robsonsmartins/usbflashprog/docs/firmware/html/a00003.png

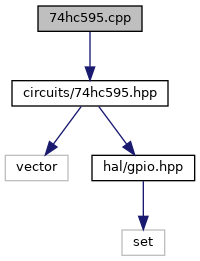
docs/firmware/html/a00003.png
