robsonsmartins/usbflashprog/docs/firmware/html/a00006.png

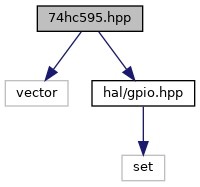
docs/firmware/html/a00006.png
