robsonsmartins/usbflashprog/docs/firmware/html/a00012.png

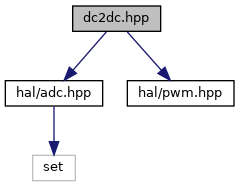
docs/firmware/html/a00012.png
