robsonsmartins/usbflashprog/docs/firmware/html/a00015.png

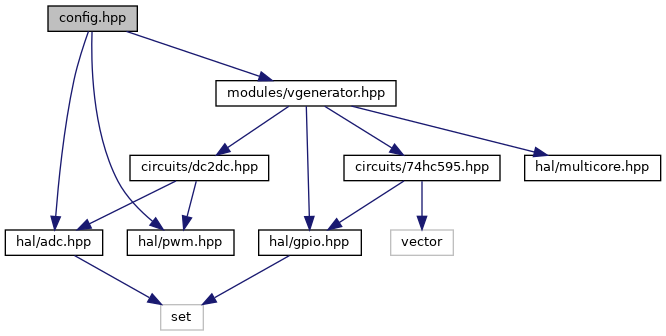
docs/firmware/html/a00015.png
