robsonsmartins/usbflashprog/docs/firmware/html/a00048.png

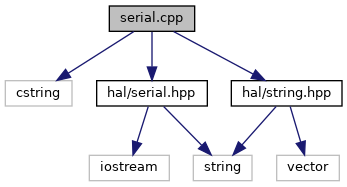
docs/firmware/html/a00048.png
