robsonsmartins/usbflashprog/docs/firmware/html/a00060.png

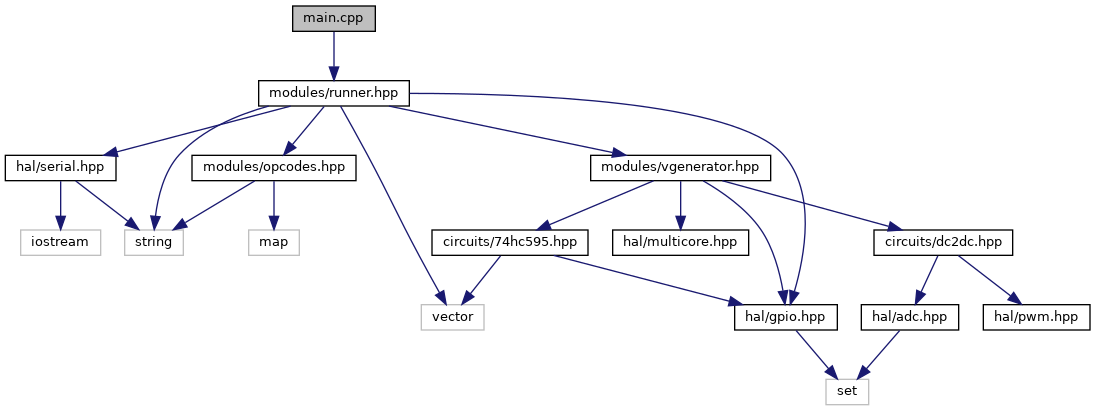
docs/firmware/html/a00060.png
