robsonsmartins/usbflashprog/docs/firmware/html/a00063.png

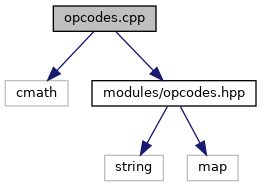
docs/firmware/html/a00063.png
