robsonsmartins/usbflashprog/docs/firmware/html/a00069.png

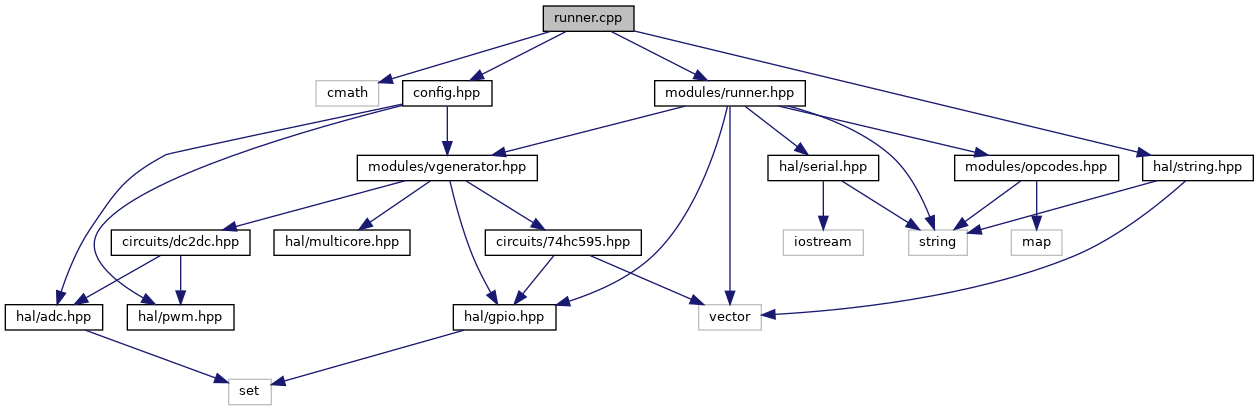
docs/firmware/html/a00069.png
