robsonsmartins/usbflashprog/docs/firmware/html/a00075.png

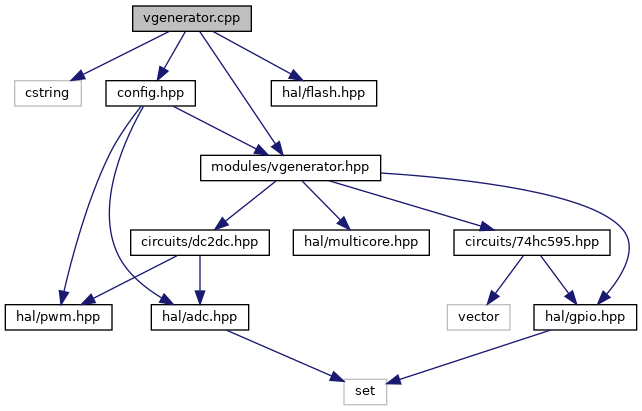
docs/firmware/html/a00075.png
