robsonsmartins/usbflashprog/docs/firmware/html/a00078.png

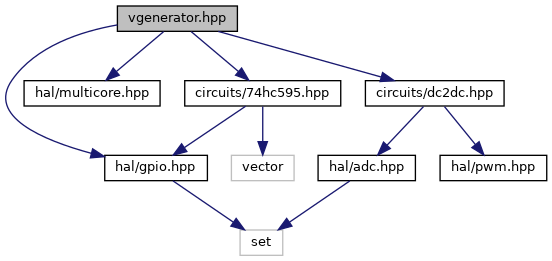
docs/firmware/html/a00078.png
