robsonsmartins/usbflashprog/docs/firmware/html/a00084.png

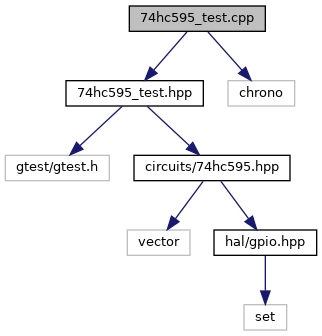
docs/firmware/html/a00084.png
