robsonsmartins/usbflashprog/docs/firmware/html/a00087.png

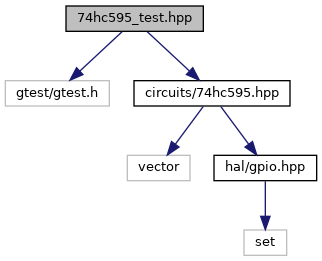
docs/firmware/html/a00087.png
