robsonsmartins/usbflashprog/docs/firmware/html/a00096.png

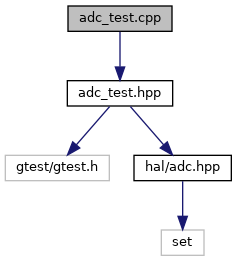
docs/firmware/html/a00096.png
