robsonsmartins/usbflashprog/docs/firmware/html/a00099.png

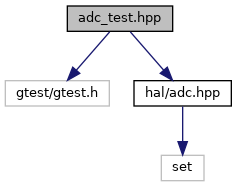
docs/firmware/html/a00099.png
