robsonsmartins/usbflashprog/docs/firmware/html/a00102.png

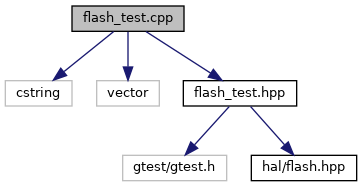
docs/firmware/html/a00102.png
