robsonsmartins/usbflashprog/docs/firmware/html/a00114.png

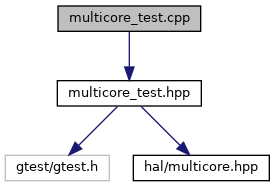
docs/firmware/html/a00114.png
