robsonsmartins/usbflashprog/docs/firmware/html/a00120.png

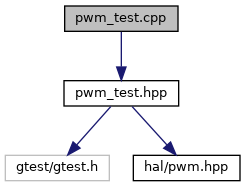
docs/firmware/html/a00120.png
