robsonsmartins/usbflashprog/docs/firmware/html/a00126.png

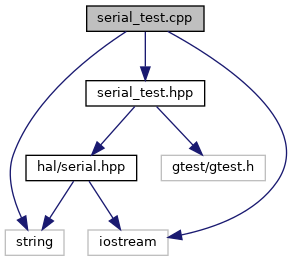
docs/firmware/html/a00126.png
