robsonsmartins/usbflashprog/docs/firmware/html/a00129.png

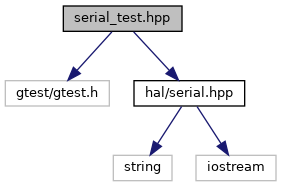
docs/firmware/html/a00129.png
