robsonsmartins/usbflashprog/docs/firmware/html/a00132.png

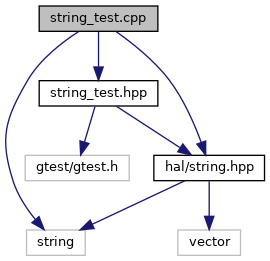
docs/firmware/html/a00132.png
