robsonsmartins/usbflashprog/docs/firmware/html/a00135.png

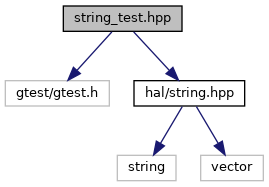
docs/firmware/html/a00135.png
