robsonsmartins/usbflashprog/docs/firmware/html/a00165.png

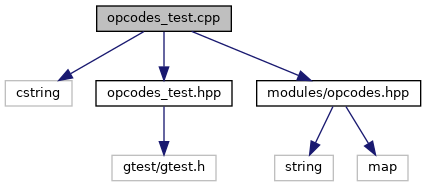
docs/firmware/html/a00165.png
