robsonsmartins/usbflashprog/docs/firmware/html/a00171.png

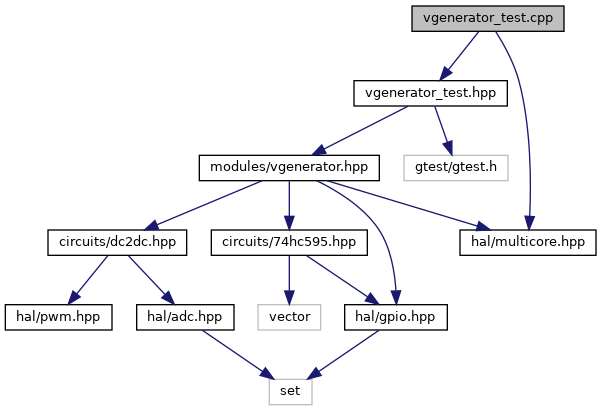
docs/firmware/html/a00171.png
