robsonsmartins/usbflashprog/docs/firmware/html/a00174.png

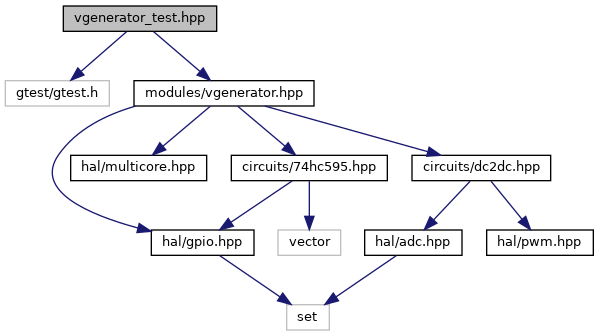
docs/firmware/html/a00174.png
