robsonsmartins/usbflashprog/docs/firmware/html/a00944.png

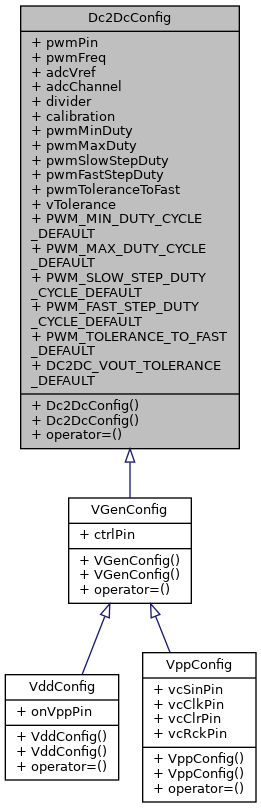
docs/firmware/html/a00944.png
