robsonsmartins/usbflashprog/docs/firmware/html/a00976.png

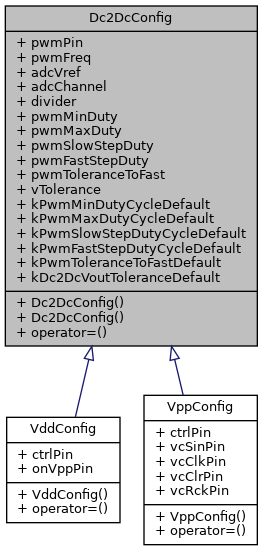
docs/firmware/html/a00976.png
