robsonsmartins/usbflashprog/docs/firmware/html/a01045.png

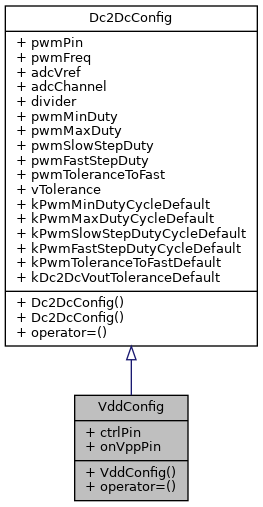
docs/firmware/html/a01045.png
