robsonsmartins/usbflashprog/docs/firmware/html/a01049.png

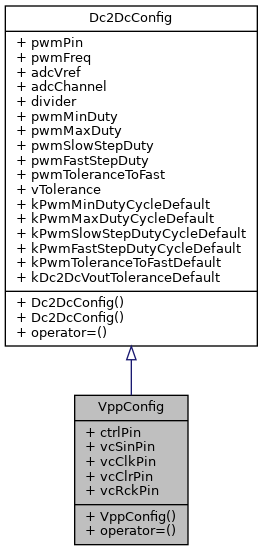
docs/firmware/html/a01049.png
