robsonsmartins/usbflashprog/docs/firmware/html/a01057.png

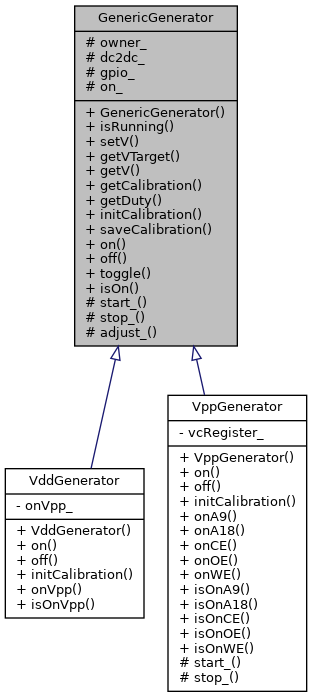
docs/firmware/html/a01057.png
