robsonsmartins/usbflashprog/docs/firmware/html/dir_73c31730a899c84a7a5c88cb9143c198_dep.png

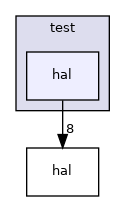
docs/firmware/html/dir_73c31730a899c84a7a5c88cb9143c198_dep.png
