robsonsmartins/usbflashprog/docs/firmware/html/dir_e05d7e2b1ecd646af5bb94391405f3b5_dep.png

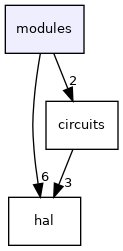
docs/firmware/html/dir_e05d7e2b1ecd646af5bb94391405f3b5_dep.png
