robsonsmartins/usbflashprog/docs/firmware/html/dir_fb26c1e57a9d2d92e8844fee7346a524_dep.png

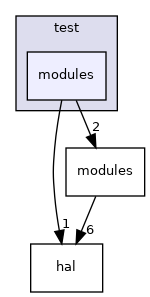
docs/firmware/html/dir_fb26c1e57a9d2d92e8844fee7346a524_dep.png
