robsonsmartins/usbflashprog/docs/software/html/a00009.png

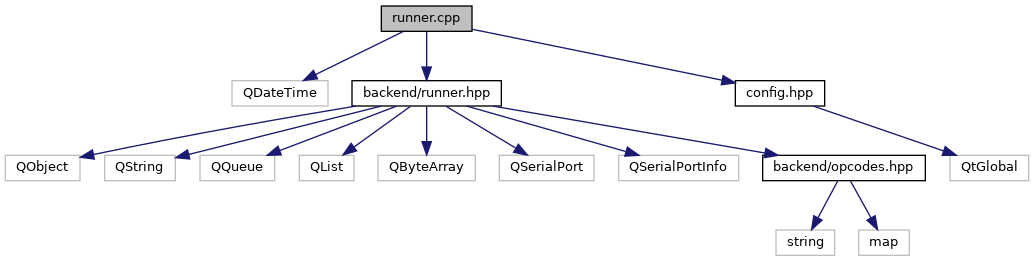
docs/software/html/a00009.png
