robsonsmartins/usbflashprog/docs/software/html/a00018.png

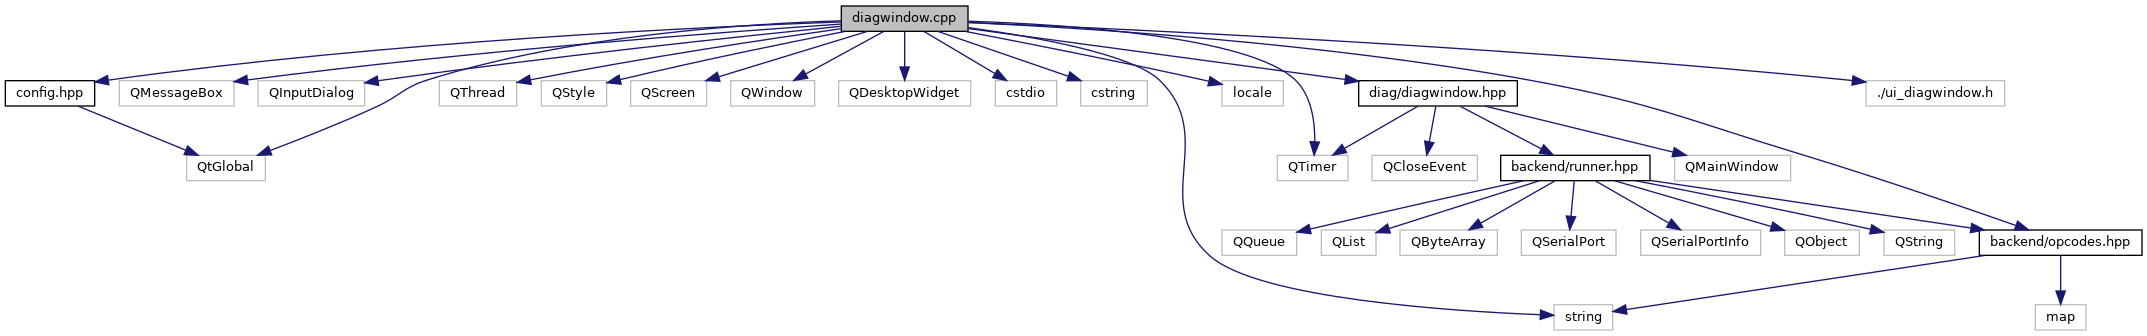
docs/software/html/a00018.png
