robsonsmartins/usbflashprog/docs/software/html/a00021.png

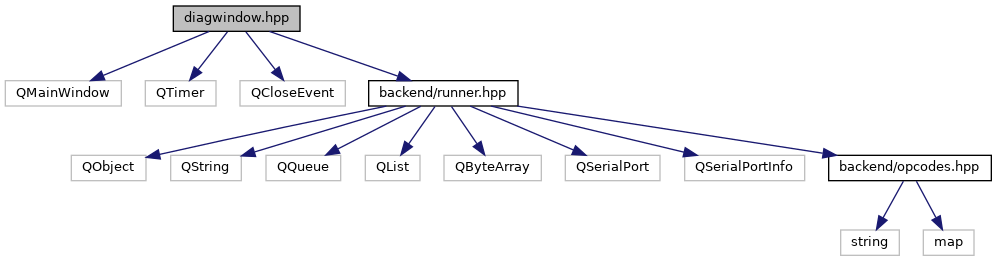
docs/software/html/a00021.png
