robsonsmartins/usbflashprog/docs/software/html/a00024.png

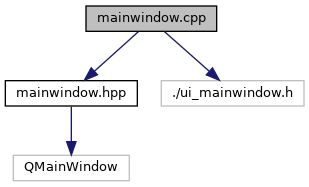
docs/software/html/a00024.png
