robsonsmartins/usbflashprog/docs/software/html/a00030.png

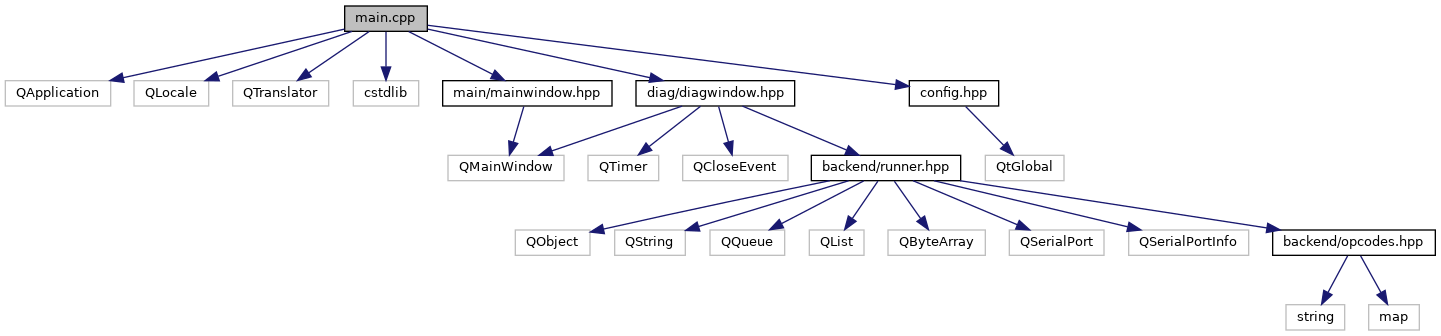
docs/software/html/a00030.png
