robsonsmartins/usbflashprog/docs/software/html/dir_13e138d54eb8818da29c3992edef070a_dep.png

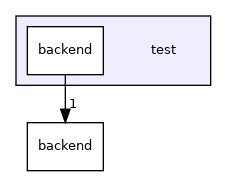
docs/software/html/dir_13e138d54eb8818da29c3992edef070a_dep.png
