robsonsmartins/usbflashprog/software/usbflashprog/scripts/ufprog.bmp

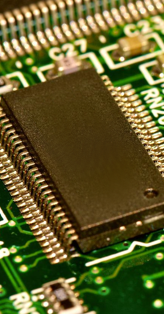
software/usbflashprog/scripts/ufprog.bmp
