robsonsmartins/usbflashprog/hardware/usbflashprog.kicad_pcb

## KiCad design hardware/usbflashprog.kicad_pcb (2022-05-16)

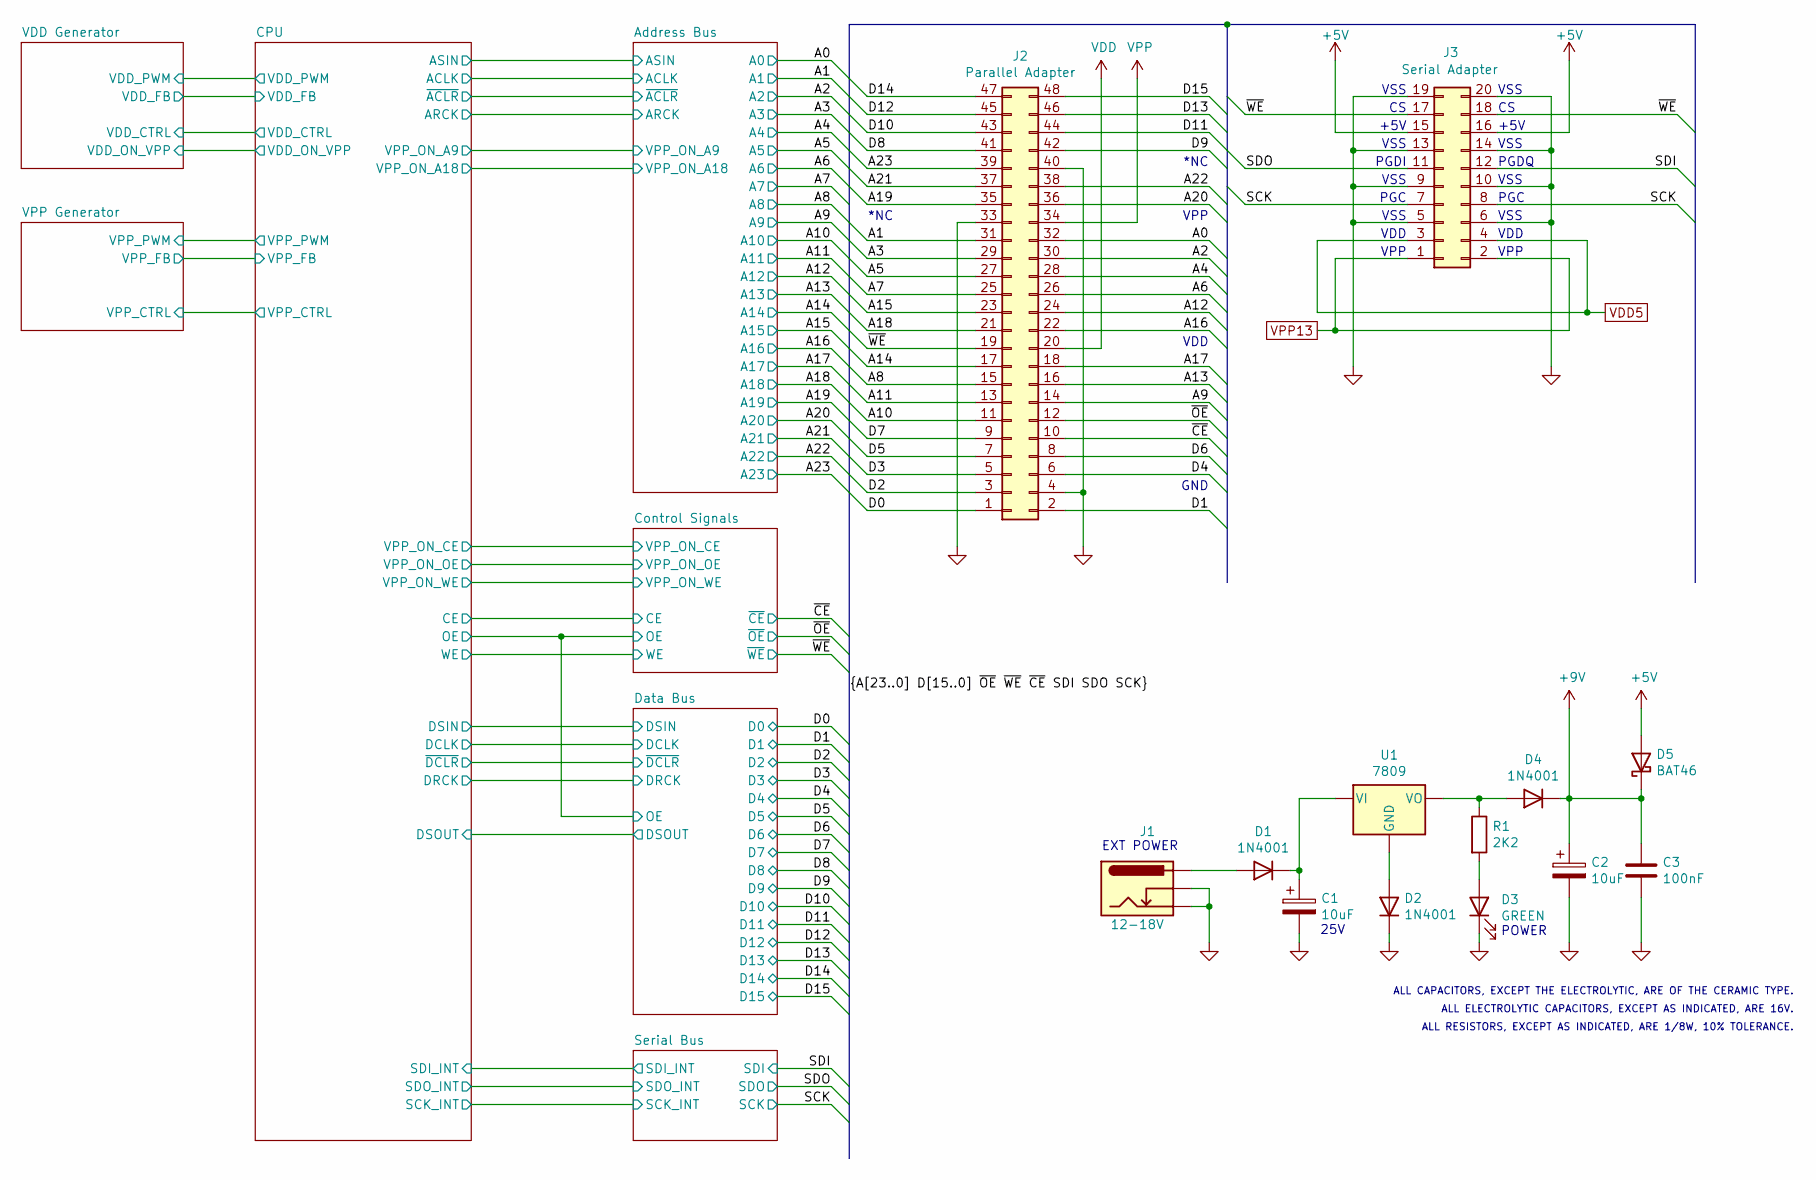
[picture p56: schematic usbflashprog.kicad_sch, USB Flash/EPROM Programmer]

Parts:
C1, C2: 10uF; CP_Radial_D5.0mm_P2.50mm
C3: 100nF; C_Disc_D6.0mm_W2.5mm_P5.00mm
D1, D2, D4: 1N4001; D_DO-41_SOD81_P10.16mm_Horizontal
D3: GREEN; LED_D3.0mm
D5: BAT46; D_DO-35_SOD27_P7.62mm_Horizontal
J1: 12-18V; BarrelJack_Horizontal
J2: Parallel Adapter; PinSocket_2x24_P2.54mm_Vertical
J3: Serial Adapter; PinSocket_2x10_P2.54mm_Vertical
R1: 2K2; R_Axial_DIN0207_L6.3mm_D2.5mm_P10.16mm_Horizontal
U1: 7809; TO-220-3_Vertical

Connections:
+5V: D5.2 (A), J3.15, J3.16; also elsewhere on the board
+9V: C2.1, C3.1, D4.1 (K), D5.1 (K); also elsewhere on the board
/A0: J2.32; also elsewhere on the board
/A1: J2.31; also elsewhere on the board
/A2: J2.30; also elsewhere on the board
/A3: J2.29; also elsewhere on the board
/A4: J2.28; also elsewhere on the board
/A5: J2.27; also elsewhere on the board
/A6: J2.26; also elsewhere on the board
/A7: J2.25; also elsewhere on the board
/A8: J2.15; also elsewhere on the board
/A9: J2.14; also elsewhere on the board
/A10: J2.11; also elsewhere on the board
/A11: J2.13; also elsewhere on the board
/A12: J2.24; also elsewhere on the board
/A13: J2.16; also elsewhere on the board
/A14: J2.17; also elsewhere on the board
/A15: J2.23; also elsewhere on the board
/A16: J2.22; also elsewhere on the board
/A17: J2.18; also elsewhere on the board
/A18: J2.21; also elsewhere on the board
/A19: J2.35; also elsewhere on the board
/A20: J2.36; also elsewhere on the board
/A21: J2.37; also elsewhere on the board
/A22: J2.38; also elsewhere on the board
/A23: J2.39; also elsewhere on the board
/D0: J2.1; also elsewhere on the board
/D1: J2.2; also elsewhere on the board
/D2: J2.3; also elsewhere on the board
/D3: J2.5; also elsewhere on the board
/D4: J2.6; also elsewhere on the board
/D5: J2.7; also elsewhere on the board
/D6: J2.8; also elsewhere on the board
/D7: J2.9; also elsewhere on the board
/D8: J2.41; also elsewhere on the board
/D9: J2.42; also elsewhere on the board
/D10: J2.43; also elsewhere on the board
/D11: J2.44; also elsewhere on the board
/D12: J2.45; also elsewhere on the board
/D13: J2.46; also elsewhere on the board
/D14: J2.47; also elsewhere on the board
/D15: J2.48; also elsewhere on the board
/SCK: J3.7, J3.8; also elsewhere on the board
/SDI: J3.12; also elsewhere on the board
/SDO: J3.11; also elsewhere on the board
/~CE: J2.10; also elsewhere on the board
/~OE: J2.12; also elsewhere on the board
/~WE: J2.19, J3.17, J3.18; also elsewhere on the board
GND: C1.2, C2.2, C3.2, D2.1 (K), D3.1 (K), J1.2, J1.3, J2.4, J2.33, J2.40, J3.5, J3.6, J3.9, J3.10, J3.13, J3.14, J3.19, J3.20; also elsewhere on the board
unnamed: C1.1, D1.1 (K), U1.1 (VI)
unnamed: D1.2 (A), J1.1
unnamed: D2.2 (A), U1.2 (GND)
unnamed: D3.2 (A), R1.2
unnamed: D4.2 (A), R1.1, U1.3 (VO)
VDD: J2.20; also elsewhere on the board
VDD5: J3.3, J3.4; also elsewhere on the board
VPP: J2.34; also elsewhere on the board
VPP13: J3.1, J3.2; also elsewhere on the board

Notes on the sheet:
EXT POWER
+5V
VSS
PGC
VPP
25V
*NC
POWER
VDD
ALL CAPACITORS, EXCEPT THE ELECTROLYTIC, ARE OF THE CERAMIC TYPE.
ALL RESISTORS, EXCEPT AS INDICATED, ARE 1/8W, 10% TOLERANCE.
PGDI
PGDQ
GND
ALL ELECTROLYTIC CAPACITORS, EXCEPT AS INDICATED, ARE 16V.

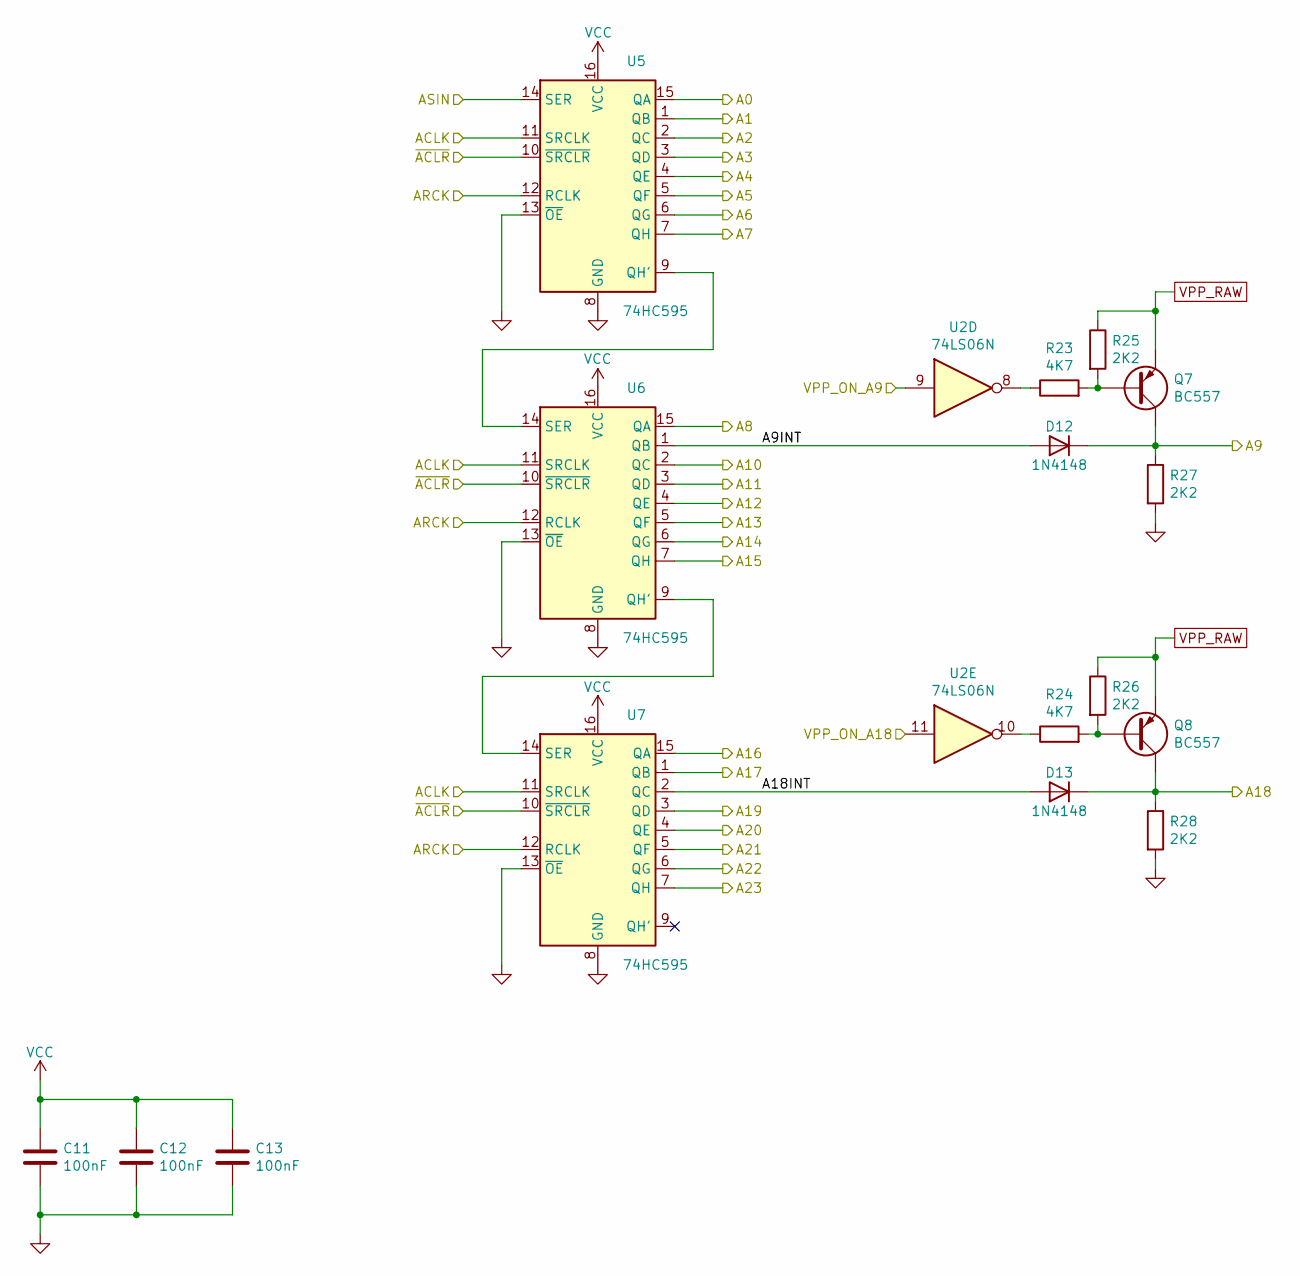
[picture p57: schematic address_bus.kicad_sch, USB Flash/EPROM Programmer]

Parts:
C11, C12, C13: 100nF; C_Disc_D6.0mm_W2.5mm_P5.00mm
D12, D13: 1N4148; D_DO-35_SOD27_P7.62mm_Horizontal
Q7, Q8: BC557; TO-92_Inline_Wide
R23, R24: 4K7; R_Axial_DIN0207_L6.3mm_D2.5mm_P10.16mm_Horizontal
R25, R26, R27, R28: 2K2; R_Axial_DIN0207_L6.3mm_D2.5mm_P10.16mm_Horizontal
U2: 74LS06N; DIP-14_W7.62mm
U5, U6, U7: 74HC595; DIP-16_W7.62mm

Connections:
/A0: U5.15 (QA); also elsewhere on the board
/A1: U5.1 (QB); also elsewhere on the board
/A2: U5.2 (QC); also elsewhere on the board
/A3: U5.3 (QD); also elsewhere on the board
/A4: U5.4 (QE); also elsewhere on the board
/A5: U5.5 (QF); also elsewhere on the board
/A6: U5.6 (QG); also elsewhere on the board
/A7: U5.7 (QH); also elsewhere on the board
/A8: U6.15 (QA); also elsewhere on the board
/A9: D12.1 (K), Q7.1 (C), R27.1; also elsewhere on the board
/A10: U6.2 (QC); also elsewhere on the board
/A11: U6.3 (QD); also elsewhere on the board
/A12: U6.4 (QE); also elsewhere on the board
/A13: U6.5 (QF); also elsewhere on the board
/A14: U6.6 (QG); also elsewhere on the board
/A15: U6.7 (QH); also elsewhere on the board
/A16: U7.15 (QA); also elsewhere on the board
/A17: U7.1 (QB); also elsewhere on the board
/A18: D13.1 (K), Q8.1 (C), R28.1; also elsewhere on the board
/A19: U7.3 (QD); also elsewhere on the board
/A20: U7.4 (QE); also elsewhere on the board
/A21: U7.5 (QF); also elsewhere on the board
/A22: U7.6 (QG); also elsewhere on the board
/A23: U7.7 (QH); also elsewhere on the board
/Address Bus/A9INT: D12.2 (A), U6.1 (QB)
/Address Bus/A18INT: D13.2 (A), U7.2 (QC)
/Address Bus/ACLK: U5.11 (SRCLK), U6.11 (SRCLK), U7.11 (SRCLK); also elsewhere on the board
/Address Bus/ARCK: U5.12 (RCLK), U6.12 (RCLK), U7.12 (RCLK); also elsewhere on the board
/Address Bus/ASIN: U5.14 (SER); also elsewhere on the board
/Address Bus/VPP_ON_A9: U2.9; also elsewhere on the board
/Address Bus/VPP_ON_A18: U2.11; also elsewhere on the board
/Address Bus/~ACLR: U5.10 (~SRCLR), U6.10 (~SRCLR), U7.10 (~SRCLR); also elsewhere on the board
GND: C11.2, C12.2, C13.2, R27.2, R28.2, U5.8 (GND), U5.13 (~OE), U6.8 (GND), U6.13 (~OE), U7.8 (GND), U7.13 (~OE); also elsewhere on the board
unnamed: Q7.2 (B), R23.2, R25.2
unnamed: Q8.2 (B), R24.2, R26.2
unnamed: R23.1, U2.8
unnamed: R24.1, U2.10
unnamed: U5.9 (QH'), U6.14 (SER)
unnamed: U6.9 (QH'), U7.14 (SER)
VCC: C11.1, C12.1, C13.1, U5.16 (VCC), U6.16 (VCC), U7.16 (VCC); also elsewhere on the board
VPP_RAW: Q7.3 (E), Q8.3 (E), R25.1, R26.1; also elsewhere on the board

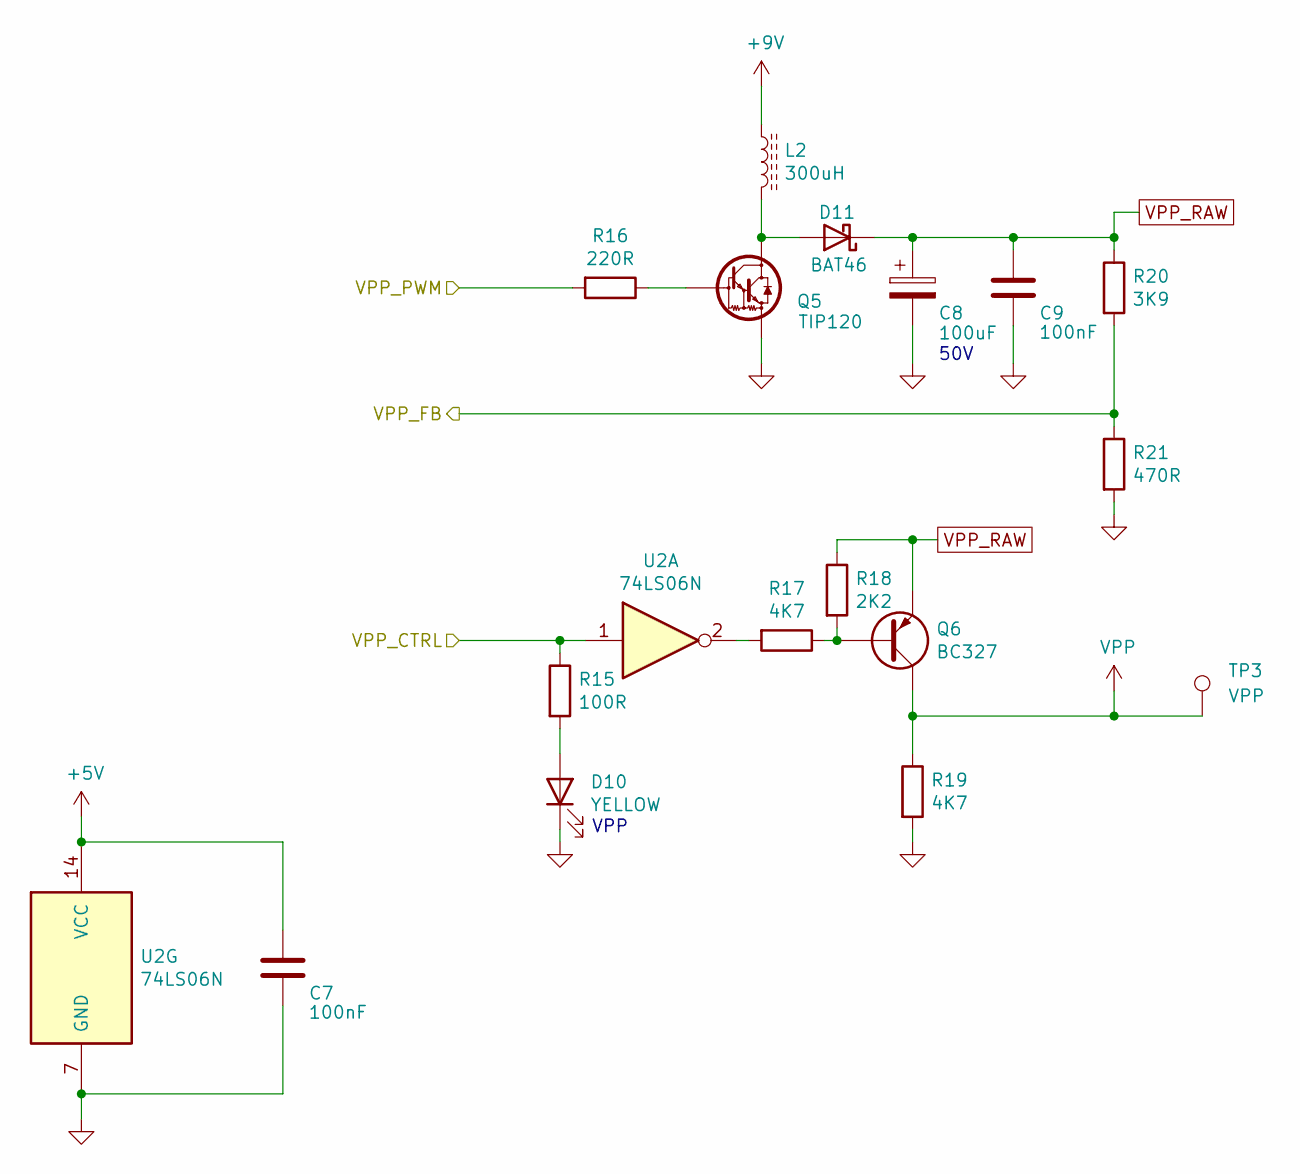
[picture p58: schematic vpp_generator.kicad_sch, USB Flash/EPROM Programmer]

Parts:
C7, C9: 100nF; C_Disc_D6.0mm_W2.5mm_P5.00mm
C8: 100uF; CP_Radial_D8.0mm_P3.50mm
D10: YELLOW; LED_D3.0mm
D11: BAT46; D_DO-35_SOD27_P7.62mm_Horizontal
L2: 300uH; L_Toroid_Vertical_L13.0mm_W6.5mm_P5.60mm
Q5: TIP120; TO-220-3_Vertical
Q6: BC327; TO-92_Inline_Wide
R15: 100R; R_Axial_DIN0207_L6.3mm_D2.5mm_P10.16mm_Horizontal
R16: 220R; R_Axial_DIN0207_L6.3mm_D2.5mm_P10.16mm_Horizontal
R17, R19: 4K7; R_Axial_DIN0207_L6.3mm_D2.5mm_P10.16mm_Horizontal
R18: 2K2; R_Axial_DIN0207_L6.3mm_D2.5mm_P10.16mm_Horizontal
R20: 3K9; R_Axial_DIN0207_L6.3mm_D2.5mm_P10.16mm_Horizontal
R21: 470R; R_Axial_DIN0207_L6.3mm_D2.5mm_P10.16mm_Horizontal
TP3: VPP; TestPoint_THTPad_2.5x2.5mm_Drill1.2mm
U2: 74LS06N; DIP-14_W7.62mm

Connections:
+5V: C7.1, U2.14 (VCC); also elsewhere on the board
+9V: L2.1; also elsewhere on the board
/CPU/VPP_CTRL: R15.1, U2.1; also elsewhere on the board
/CPU/VPP_FB: R20.2, R21.1; also elsewhere on the board
/CPU/VPP_PWM: R16.2; also elsewhere on the board
GND: C7.2, C8.2, C9.2, D10.1 (K), Q5.3 (E), R19.2, R21.2, U2.7 (GND); also elsewhere on the board
unnamed: D10.2 (A), R15.2
unnamed: D11.2 (A), L2.2, Q5.2 (C)
unnamed: Q5.1 (B), R16.1
unnamed: Q6.2 (B), R17.1, R18.2
unnamed: R17.2, U2.2
VPP: Q6.1 (C), R19.1, TP3.1; also elsewhere on the board
VPP_RAW: C8.1, C9.1, D11.1 (K), Q6.3 (E), R18.1, R20.1; also elsewhere on the board

Notes on the sheet:
VPP
50V

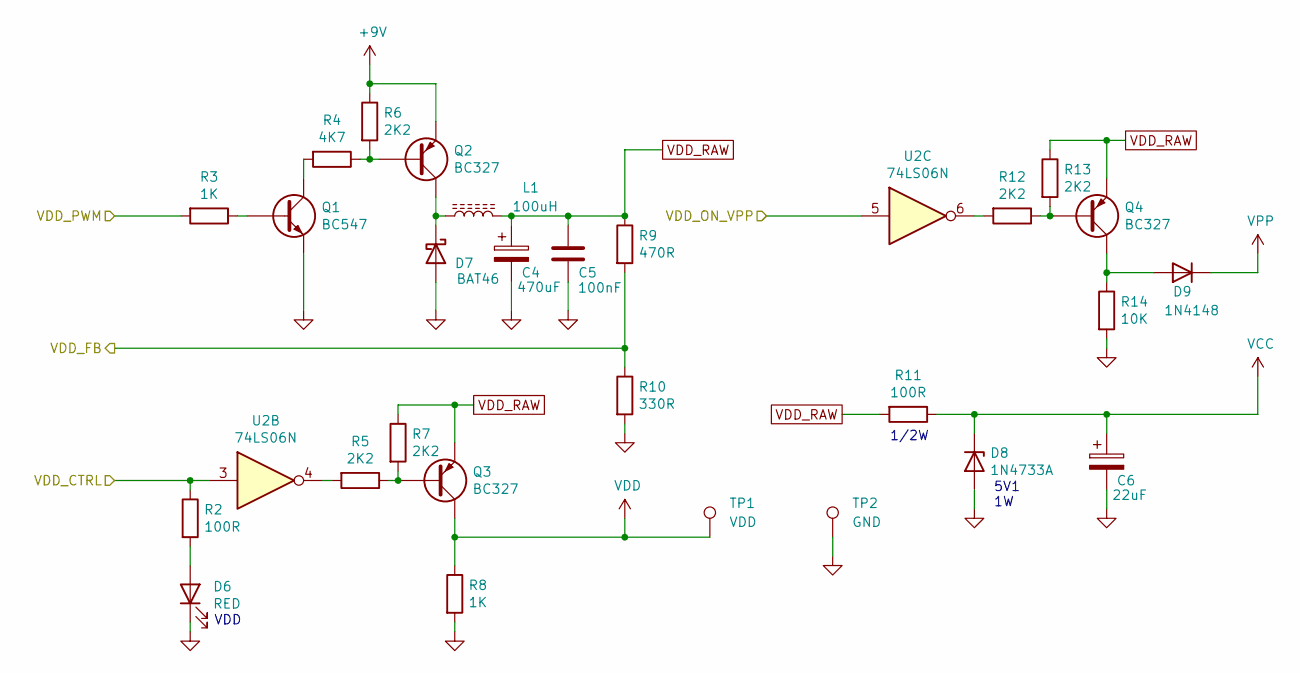
[picture p59: schematic vdd_generator.kicad_sch, USB Flash/EPROM Programmer]

Parts:
C4: 470uF; CP_Radial_D8.0mm_P3.80mm
C5: 100nF; C_Disc_D6.0mm_W2.5mm_P5.00mm
C6: 22uF; CP_Radial_D5.0mm_P2.50mm
D6: RED; LED_D3.0mm
D7: BAT46; D_DO-35_SOD27_P7.62mm_Horizontal
D8: 1N4733A; D_DO-41_SOD81_P10.16mm_Horizontal
D9: 1N4148; D_DO-35_SOD27_P7.62mm_Horizontal
L1: 100uH; L_Toroid_Vertical_L13.0mm_W6.5mm_P5.60mm
Q1: BC547; TO-92_Inline_Wide
Q2, Q3, Q4: BC327; TO-92_Inline_Wide
R2, R11: 100R; R_Axial_DIN0207_L6.3mm_D2.5mm_P10.16mm_Horizontal
R3, R8: 1K; R_Axial_DIN0207_L6.3mm_D2.5mm_P10.16mm_Horizontal
R4: 4K7; R_Axial_DIN0207_L6.3mm_D2.5mm_P10.16mm_Horizontal
R5, R6, R7, R12, R13: 2K2; R_Axial_DIN0207_L6.3mm_D2.5mm_P10.16mm_Horizontal
R9: 470R; R_Axial_DIN0207_L6.3mm_D2.5mm_P10.16mm_Horizontal
R10: 330R; R_Axial_DIN0207_L6.3mm_D2.5mm_P10.16mm_Horizontal
R14: 10K; R_Axial_DIN0207_L6.3mm_D2.5mm_P10.16mm_Horizontal
TP1: VDD; TestPoint_THTPad_2.5x2.5mm_Drill1.2mm
TP2: GND; TestPoint_THTPad_2.5x2.5mm_Drill1.2mm
U2: 74LS06N; DIP-14_W7.62mm

Connections:
+9V: Q2.3 (E), R6.1; also elsewhere on the board
/CPU/VDD_CTRL: R2.1, U2.3; also elsewhere on the board
/CPU/VDD_FB: R9.2, R10.1; also elsewhere on the board
/CPU/VDD_ON_VPP: U2.5; also elsewhere on the board
/CPU/VDD_PWM: R3.2; also elsewhere on the board
GND: C4.2, C5.2, C6.2, D6.1 (K), D7.2 (A), D8.2 (A), Q1.3 (E), R8.2, R10.2, R14.2, TP2.1; also elsewhere on the board
unnamed: D6.2 (A), R2.2
unnamed: D7.1 (K), L1.1, Q2.1 (C)
unnamed: D9.2 (A), Q4.1 (C), R14.1
unnamed: Q1.1 (C), R4.2
unnamed: Q1.2 (B), R3.1
unnamed: Q2.2 (B), R4.1, R6.2
unnamed: Q3.2 (B), R5.1, R7.2
unnamed: Q4.2 (B), R12.1, R13.2
unnamed: R5.2, U2.4
unnamed: R12.2, U2.6
VCC: C6.1, D8.1 (K), R11.1; also elsewhere on the board
VDD: Q3.1 (C), R8.1, TP1.1; also elsewhere on the board
VDD_RAW: C4.1, C5.1, L1.2, Q3.3 (E), Q4.3 (E), R7.1, R9.1, R11.2, R13.1; also elsewhere on the board
VPP: D9.1 (K); also elsewhere on the board

Notes on the sheet:
1/2W
5V1 1W
VDD

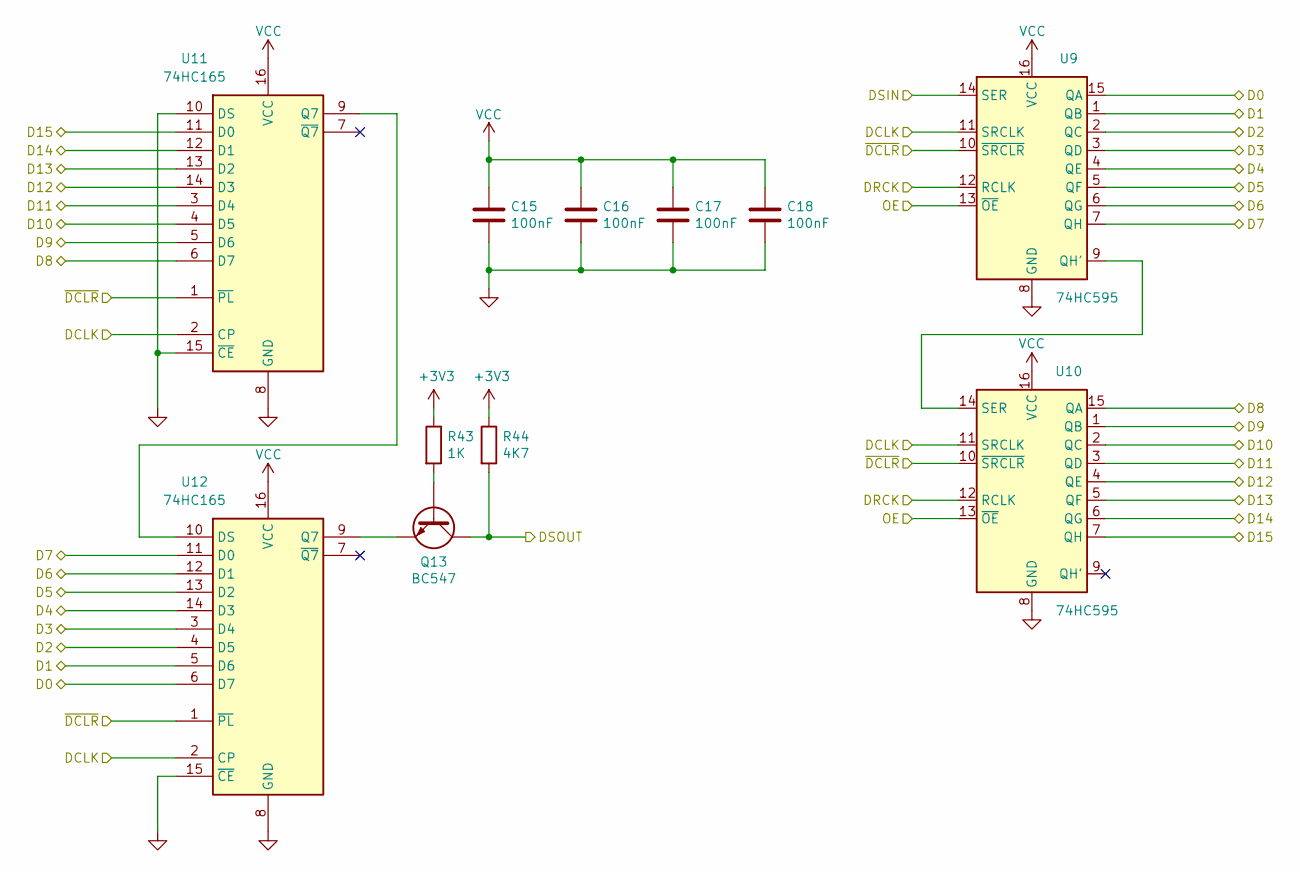
[picture p60: schematic data_bus.kicad_sch, USB Flash/EPROM Programmer]

Parts:
C15, C16, C17, C18: 100nF; C_Disc_D6.0mm_W2.5mm_P5.00mm
Q13: BC547; TO-92_Inline_Wide
R43: 1K; R_Axial_DIN0207_L6.3mm_D2.5mm_P10.16mm_Horizontal
R44: 4K7; R_Axial_DIN0207_L6.3mm_D2.5mm_P10.16mm_Horizontal
U9, U10: 74HC595; DIP-16_W7.62mm
U11, U12: 74HC165; DIP-16_W7.62mm

Connections:
+3V3: R43.1, R44.1; also elsewhere on the board
/CPU/DCLK: U9.11 (SRCLK), U10.11 (SRCLK), U11.2 (CP), U12.2 (CP); also elsewhere on the board
/CPU/DRCK: U9.12 (RCLK), U10.12 (RCLK); also elsewhere on the board
/CPU/DSIN: U9.14 (SER); also elsewhere on the board
/CPU/DSOUT: Q13.1 (C), R44.2; also elsewhere on the board
/CPU/OE: U9.13 (~OE), U10.13 (~OE); also elsewhere on the board
/CPU/~DCLR: U9.10 (~SRCLR), U10.10 (~SRCLR), U11.1 (~PL), U12.1 (~PL); also elsewhere on the board
/D0: U9.15 (QA), U12.6 (D7); also elsewhere on the board
/D1: U9.1 (QB), U12.5 (D6); also elsewhere on the board
/D2: U9.2 (QC), U12.4 (D5); also elsewhere on the board
/D3: U9.3 (QD), U12.3 (D4); also elsewhere on the board
/D4: U9.4 (QE), U12.14 (D3); also elsewhere on the board
/D5: U9.5 (QF), U12.13 (D2); also elsewhere on the board
/D6: U9.6 (QG), U12.12 (D1); also elsewhere on the board
/D7: U9.7 (QH), U12.11 (D0); also elsewhere on the board
/D8: U10.15 (QA), U11.6 (D7); also elsewhere on the board
/D9: U10.1 (QB), U11.5 (D6); also elsewhere on the board
/D10: U10.2 (QC), U11.4 (D5); also elsewhere on the board
/D11: U10.3 (QD), U11.3 (D4); also elsewhere on the board
/D12: U10.4 (QE), U11.14 (D3); also elsewhere on the board
/D13: U10.5 (QF), U11.13 (D2); also elsewhere on the board
/D14: U10.6 (QG), U11.12 (D1); also elsewhere on the board
/D15: U10.7 (QH), U11.11 (D0); also elsewhere on the board
GND: C15.2, C16.2, C17.2, C18.2, U9.8 (GND), U10.8 (GND), U11.8 (GND), U11.10 (DS), U11.15 (~CE), U12.8 (GND), U12.15 (~CE); also elsewhere on the board
unnamed: Q13.2 (B), R43.2
unnamed: Q13.3 (E), U12.9 (Q7)
unnamed: U9.9 (QH'), U10.14 (SER)
unnamed: U11.9 (Q7), U12.10 (DS)
VCC: C15.1, C16.1, C17.1, C18.1, U9.16 (VCC), U10.16 (VCC), U11.16 (VCC), U12.16 (VCC); also elsewhere on the board

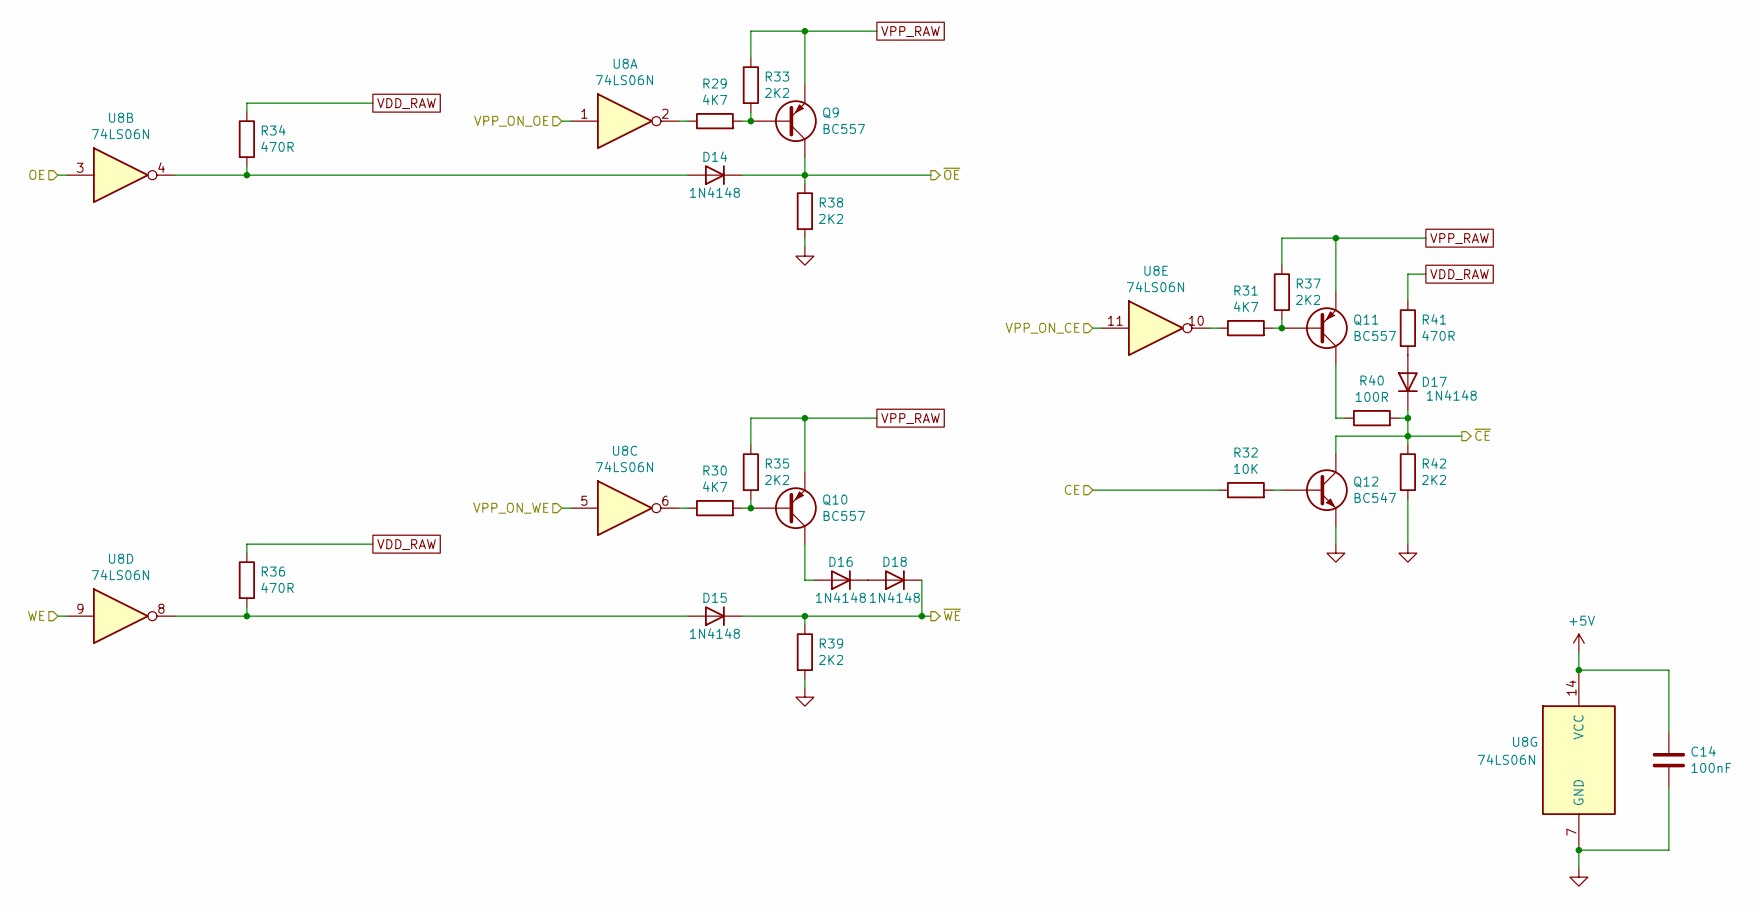
[picture p61: schematic control_signals.kicad_sch, USB Flash/EPROM Programmer]

Parts:
C14: 100nF; C_Disc_D6.0mm_W2.5mm_P5.00mm
D14, D15, D16, D17, D18: 1N4148; D_DO-35_SOD27_P7.62mm_Horizontal
Q9, Q10, Q11: BC557; TO-92_Inline_Wide
Q12: BC547; TO-92_Inline_Wide
R29, R30, R31: 4K7; R_Axial_DIN0207_L6.3mm_D2.5mm_P10.16mm_Horizontal
R32: 10K; R_Axial_DIN0207_L6.3mm_D2.5mm_P10.16mm_Horizontal
R33, R35, R37, R38, R39, R42: 2K2; R_Axial_DIN0207_L6.3mm_D2.5mm_P10.16mm_Horizontal
R34, R36, R41: 470R; R_Axial_DIN0207_L6.3mm_D2.5mm_P10.16mm_Horizontal
R40: 100R; R_Axial_DIN0207_L6.3mm_D2.5mm_P10.16mm_Horizontal
U8: 74LS06N; DIP-14_W7.62mm

Connections:
+5V: C14.1, U8.14 (VCC); also elsewhere on the board
/CPU/CE: R32.1; also elsewhere on the board
/CPU/OE: U8.3; also elsewhere on the board
/CPU/VPP_ON_CE: U8.11; also elsewhere on the board
/CPU/VPP_ON_OE: U8.1; also elsewhere on the board
/CPU/VPP_ON_WE: U8.5; also elsewhere on the board
/CPU/WE: U8.9; also elsewhere on the board
/~CE: D17.1 (K), Q12.1 (C), R40.2, R42.1; also elsewhere on the board
/~OE: D14.1 (K), Q9.1 (C), R38.1; also elsewhere on the board
/~WE: D15.1 (K), D18.1 (K), R39.1; also elsewhere on the board
GND: C14.2, Q12.3 (E), R38.2, R39.2, R42.2, U8.7 (GND); also elsewhere on the board
unnamed: D14.2 (A), R34.2, U8.4
unnamed: D15.2 (A), R36.2, U8.8
unnamed: D16.1 (K), D18.2 (A)
unnamed: D16.2 (A), Q10.1 (C)
unnamed: D17.2 (A), R41.2
unnamed: Q9.2 (B), R29.2, R33.2
unnamed: Q10.2 (B), R30.2, R35.2
unnamed: Q11.1 (C), R40.1
unnamed: Q11.2 (B), R31.2, R37.2
unnamed: Q12.2 (B), R32.2
unnamed: R29.1, U8.2
unnamed: R30.1, U8.6
unnamed: R31.1, U8.10
VDD_RAW: R34.1, R36.1, R41.1; also elsewhere on the board
VPP_RAW: Q9.3 (E), Q10.3 (E), Q11.3 (E), R33.1, R35.1, R37.1; also elsewhere on the board

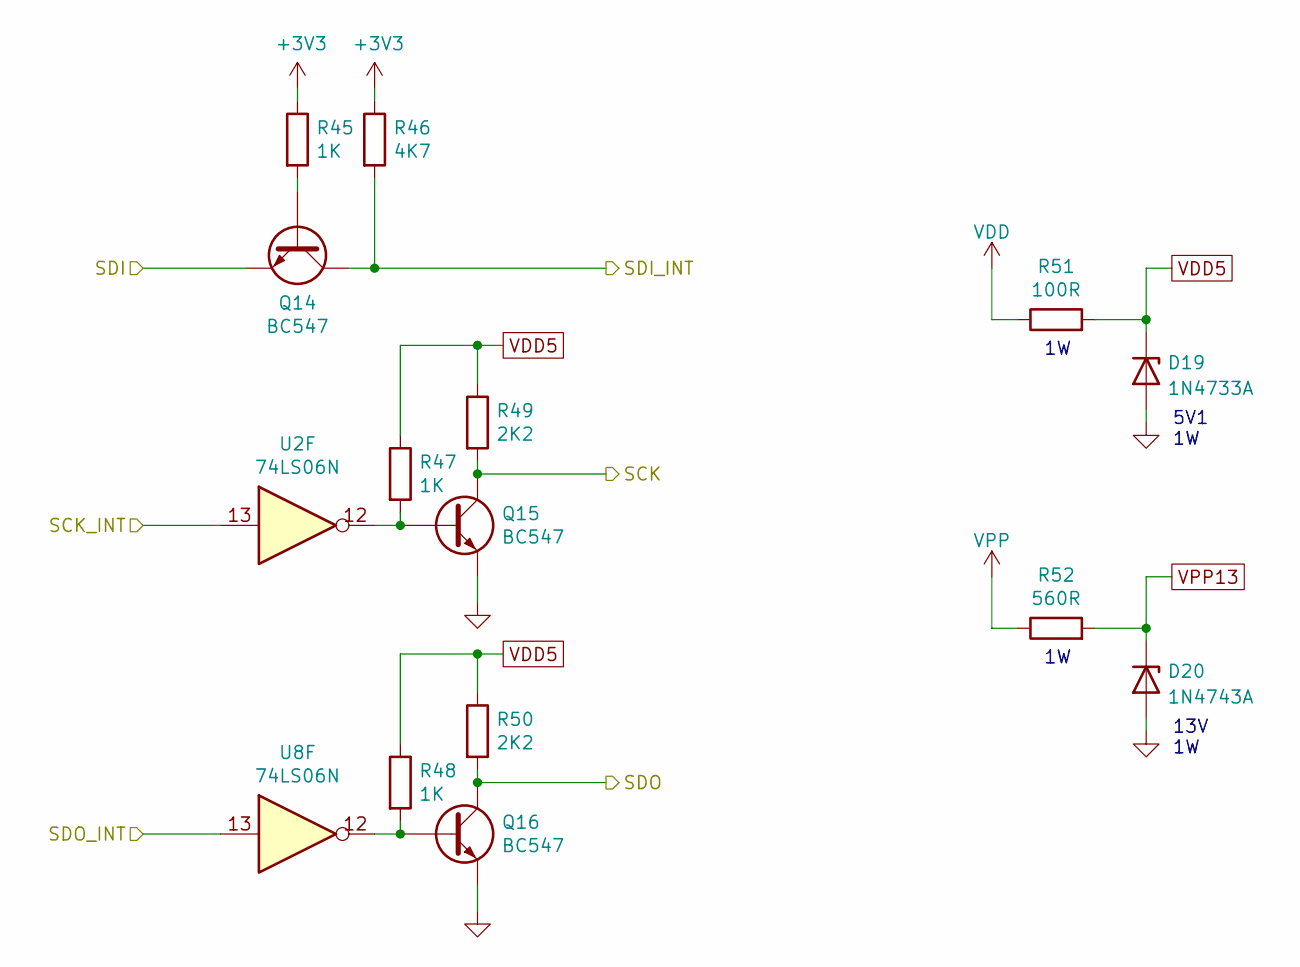
[picture p62: schematic serial_bus.kicad_sch, USB Flash/EPROM Programmer]

Parts:
D19: 1N4733A; D_DO-41_SOD81_P10.16mm_Horizontal
D20: 1N4743A; D_DO-41_SOD81_P10.16mm_Horizontal
Q14, Q15, Q16: BC547; TO-92_Inline_Wide
R45, R47, R48: 1K; R_Axial_DIN0207_L6.3mm_D2.5mm_P10.16mm_Horizontal
R46: 4K7; R_Axial_DIN0207_L6.3mm_D2.5mm_P10.16mm_Horizontal
R49, R50: 2K2; R_Axial_DIN0207_L6.3mm_D2.5mm_P10.16mm_Horizontal
R51: 100R; R_Axial_DIN0207_L6.3mm_D2.5mm_P10.16mm_Horizontal
R52: 560R; R_Axial_DIN0309_L9.0mm_D3.2mm_P15.24mm_Horizontal
U2, U8: 74LS06N; DIP-14_W7.62mm

Connections:
+3V3: R45.1, R46.1; also elsewhere on the board
/CPU/SCK_INT: U2.13; also elsewhere on the board
/CPU/SDI_INT: Q14.1 (C), R46.2; also elsewhere on the board
/CPU/SDO_INT: U8.13; also elsewhere on the board
/SCK: Q15.1 (C), R49.2; also elsewhere on the board
/SDI: Q14.3 (E); also elsewhere on the board
/SDO: Q16.1 (C), R50.2; also elsewhere on the board
GND: D19.2 (A), D20.2 (A), Q15.3 (E), Q16.3 (E); also elsewhere on the board
unnamed: Q14.2 (B), R45.2
unnamed: Q15.2 (B), R47.2, U2.12
unnamed: Q16.2 (B), R48.2, U8.12
VDD: R51.1; also elsewhere on the board
VDD5: D19.1 (K), R47.1, R48.1, R49.1, R50.1, R51.2; also elsewhere on the board
VPP: R52.1; also elsewhere on the board
VPP13: D20.1 (K), R52.2; also elsewhere on the board

Notes on the sheet:
13V 1W
5V1 1W

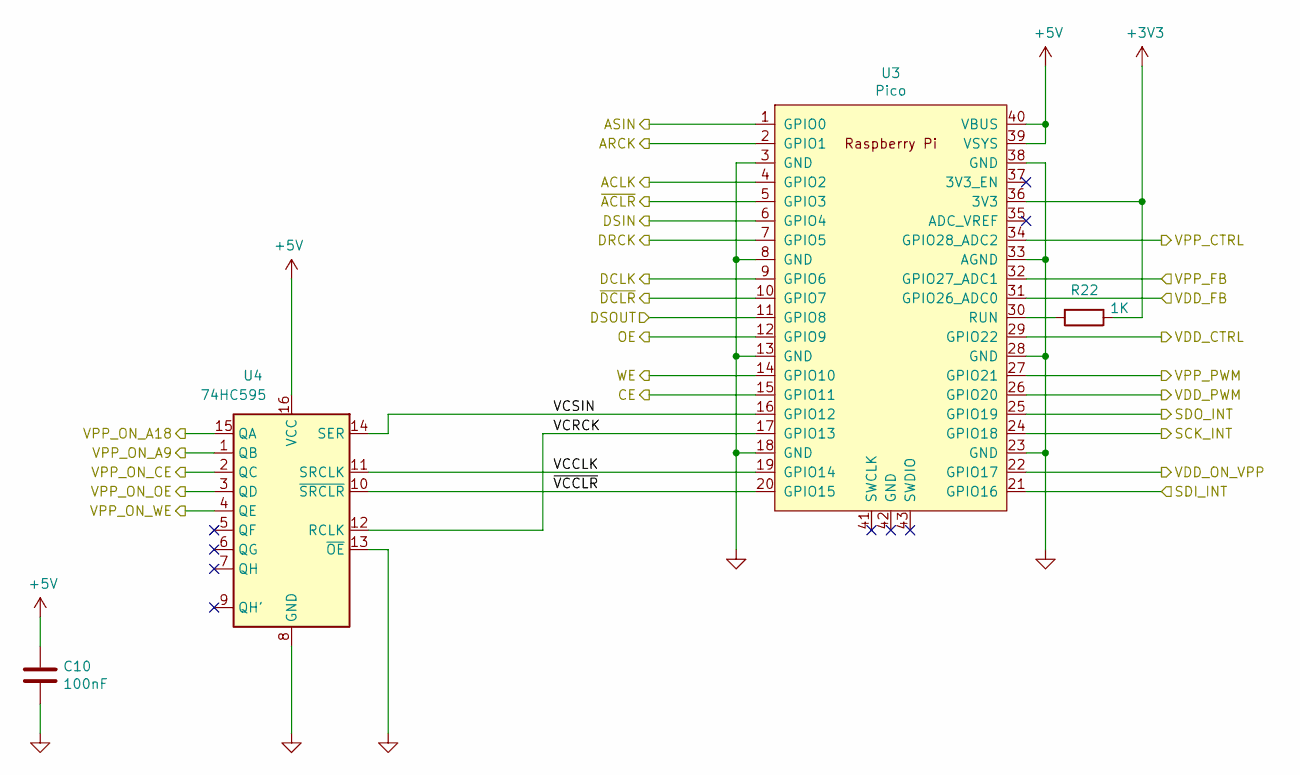
[picture p63: schematic cpu.kicad_sch, USB Flash/EPROM Programmer]

Parts:
C10: 100nF; C_Disc_D6.0mm_W2.5mm_P5.00mm
R22: 1K; R_Axial_DIN0207_L6.3mm_D2.5mm_P10.16mm_Horizontal
U3: Pico; RPi_Pico_SMD_TH
U4: 74HC595; DIP-16_W7.62mm

Connections:
+3V3: R22.1, U3.36 (3V3); also elsewhere on the board
+5V: C10.1, U3.39 (VSYS), U3.40 (VBUS), U4.16 (VCC); also elsewhere on the board
/Address Bus/ACLK: U3.4 (GPIO2); also elsewhere on the board
/Address Bus/ARCK: U3.2 (GPIO1); also elsewhere on the board
/Address Bus/ASIN: U3.1 (GPIO0); also elsewhere on the board
/Address Bus/VPP_ON_A9: U4.1 (QB); also elsewhere on the board
/Address Bus/VPP_ON_A18: U4.15 (QA); also elsewhere on the board
/Address Bus/~ACLR: U3.5 (GPIO3); also elsewhere on the board
/CPU/CE: U3.15 (GPIO11); also elsewhere on the board
/CPU/DCLK: U3.9 (GPIO6); also elsewhere on the board
/CPU/DRCK: U3.7 (GPIO5); also elsewhere on the board
/CPU/DSIN: U3.6 (GPIO4); also elsewhere on the board
/CPU/DSOUT: U3.11 (GPIO8); also elsewhere on the board
/CPU/OE: U3.12 (GPIO9); also elsewhere on the board
/CPU/SCK_INT: U3.24 (GPIO18); also elsewhere on the board
/CPU/SDI_INT: U3.21 (GPIO16); also elsewhere on the board
/CPU/SDO_INT: U3.25 (GPIO19); also elsewhere on the board
/CPU/VCCLK: U3.19 (GPIO14), U4.11 (SRCLK)
/CPU/VCRCK: U3.17 (GPIO13), U4.12 (RCLK)
/CPU/VCSIN: U3.16 (GPIO12), U4.14 (SER)
/CPU/VDD_CTRL: U3.29 (GPIO22); also elsewhere on the board
/CPU/VDD_FB: U3.31 (GPIO26_ADC0); also elsewhere on the board
/CPU/VDD_ON_VPP: U3.22 (GPIO17); also elsewhere on the board
/CPU/VDD_PWM: U3.26 (GPIO20); also elsewhere on the board
/CPU/VPP_CTRL: U3.34 (GPIO28_ADC2); also elsewhere on the board
/CPU/VPP_FB: U3.32 (GPIO27_ADC1); also elsewhere on the board
/CPU/VPP_ON_CE: U4.2 (QC); also elsewhere on the board
/CPU/VPP_ON_OE: U4.3 (QD); also elsewhere on the board
/CPU/VPP_ON_WE: U4.4 (QE); also elsewhere on the board
/CPU/VPP_PWM: U3.27 (GPIO21); also elsewhere on the board
/CPU/WE: U3.14 (GPIO10); also elsewhere on the board
/CPU/~DCLR: U3.10 (GPIO7); also elsewhere on the board
/CPU/~VCCLR: U3.20 (GPIO15), U4.10 (~SRCLR)
GND: C10.2, U3.3 (GND), U3.8 (GND), U3.13 (GND), U3.18 (GND), U3.23 (GND), U3.28 (GND), U3.33 (AGND), U3.38 (GND), U4.8 (GND), U4.13 (~OE); also elsewhere on the board
unnamed: R22.2, U3.30 (RUN)

Board: 2 copper layers, 126 parts (0 on the bottom side), 137 nets, no tracks yet.
