robsonsmartins/usbflashprog/software/usbflashprog/main/mainwindow.cpp

// ---------------------------------------------------------------------------
// USB EPROM/Flash Programmer
//
// Copyright (2022) Robson Martins
//
// This work is licensed under a Creative Commons Attribution-NonCommercial-
// ShareAlike 4.0 International License.
// ---------------------------------------------------------------------------
/** 
 * @ingroup Software
 * @file main/mainwindow.cpp
 * @brief Implementation of the Main Window Class.
 *  
 * @author Robson Martins (https://www.robsonmartins.com)
 */
// ---------------------------------------------------------------------------

#include "mainwindow.hpp"
#include "./ui_mainwindow.h"

// ---------------------------------------------------------------------------

MainWindow::MainWindow(QWidget *parent)
    : QMainWindow(parent)
    , ui(new Ui::MainWindow) {
    ui->setupUi(this);
}

MainWindow::~MainWindow() {
    delete ui;
}
