robsonsmartins/usbflashprog/firmware/usbflashprog/hal/serial.cpp

// ---------------------------------------------------------------------------
// USB EPROM/Flash Programmer
//
// Copyright (2022) Robson Martins
//
// This work is licensed under a Creative Commons Attribution-NonCommercial-
// ShareAlike 4.0 International License.
// ---------------------------------------------------------------------------
/**
 * @ingroup Firmware
 * @file hal/serial.cpp
 * @brief Implementation of the Pico Serial Communication Class.
 * 
 * @author Robson Martins (https://www.robsonmartins.com)
 */
// ---------------------------------------------------------------------------

#include <cstring>

#include "hal/serial.hpp"
#include "hal/string.hpp"

// ---------------------------------------------------------------------------

Serial::Serial() {
    stdio_init_all();
}

int Serial::getChar(uint32_t us) {
    return getchar_timeout_us(us);
}

size_t Serial::getBuf(void *buf, size_t len, uint32_t us) {
    if (!buf || !len) { return 0; }
    size_t rd = 0;
    char *p = reinterpret_cast<char*>(buf);
    int c;
    do {
        if ((c = getchar_timeout_us(us)) != PICO_ERROR_TIMEOUT) {
            *p = c;
            p++;
            rd++;
        } else { break; }
    } while (rd < len);
    return rd;
}

std::string Serial::getStr(uint32_t us) {
    std::string result;
    int c;
    do {
        if ((c = getchar_timeout_us(us)) == PICO_ERROR_TIMEOUT
                || c == '\n') { break; }
        result += static_cast<char>(c);
    } while (true);
    return result;
}

int Serial::getInt(uint base, uint32_t us) {
    return StringUtils::toInt(getStr(us), base);
}

float Serial::getFloat(uint32_t us) {
    return StringUtils::toFloat(getStr(us));
}

void Serial::putChar(char c, bool flush) {
    putchar_raw(c);
    if (flush) { stdio_flush(); }
}

void Serial::putBuf(const void *src, size_t len, bool flush) {
    if (!src || !len) { return; }
    const char *p = reinterpret_cast<const char*>(src);
    for (size_t i = 0; i < len; i++) {
        putchar_raw(p[i]);
    }
    if (flush) { stdio_flush(); }
}

void Serial::putStr(const std::string &src, bool flush) {
    if (src.empty()) { return; }
    putBuf(src.data(), src.length(), flush);
}

void Serial::putInt(int src, uint base, uint digits, char fill, bool flush) {
    putStr(StringUtils::fromInt(src, base, digits, fill), flush);
}

void Serial::putFloat(float src, uint precision, bool flush) {
    putStr(StringUtils::fromFloat(src, precision), flush);
}

std::ostream& Serial::out() {
    return std::cout;
}

std::istream& Serial::in() {
    return std::cin;
}
